GalaxyGamingBoy/6502-Microcontroller/imgs/case-0.png

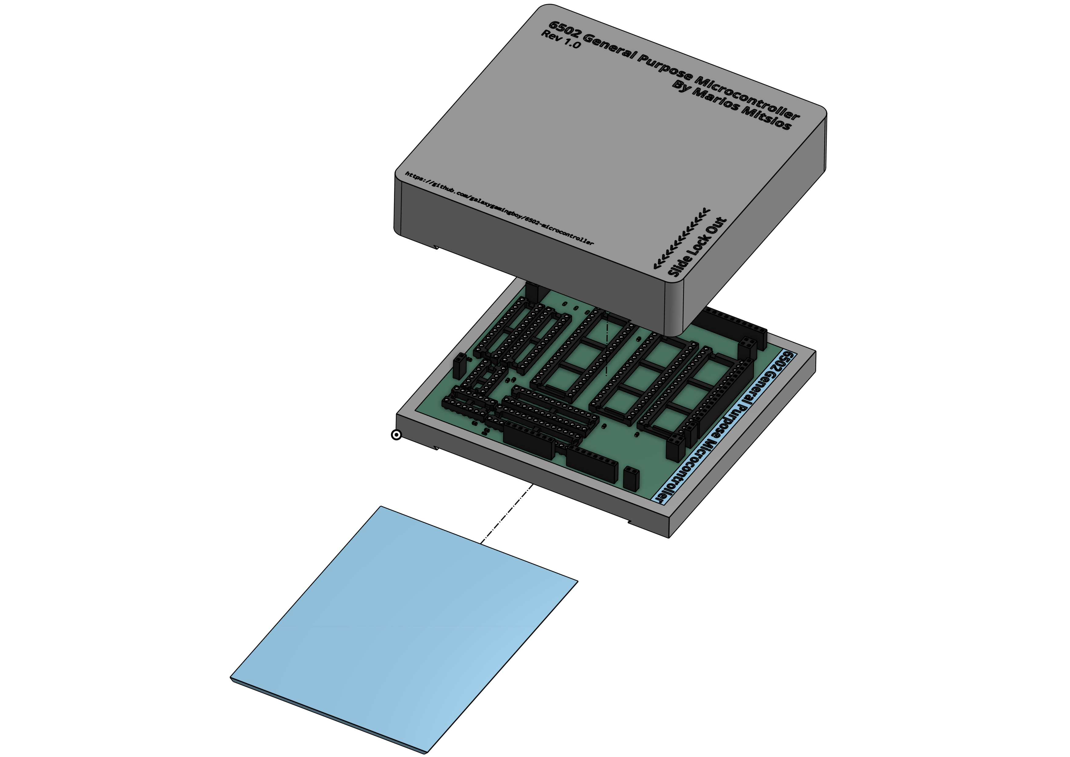
imgs/case-0.png
