GalaxyGamingBoy/6502-Microcontroller/imgs/schematic-0.png

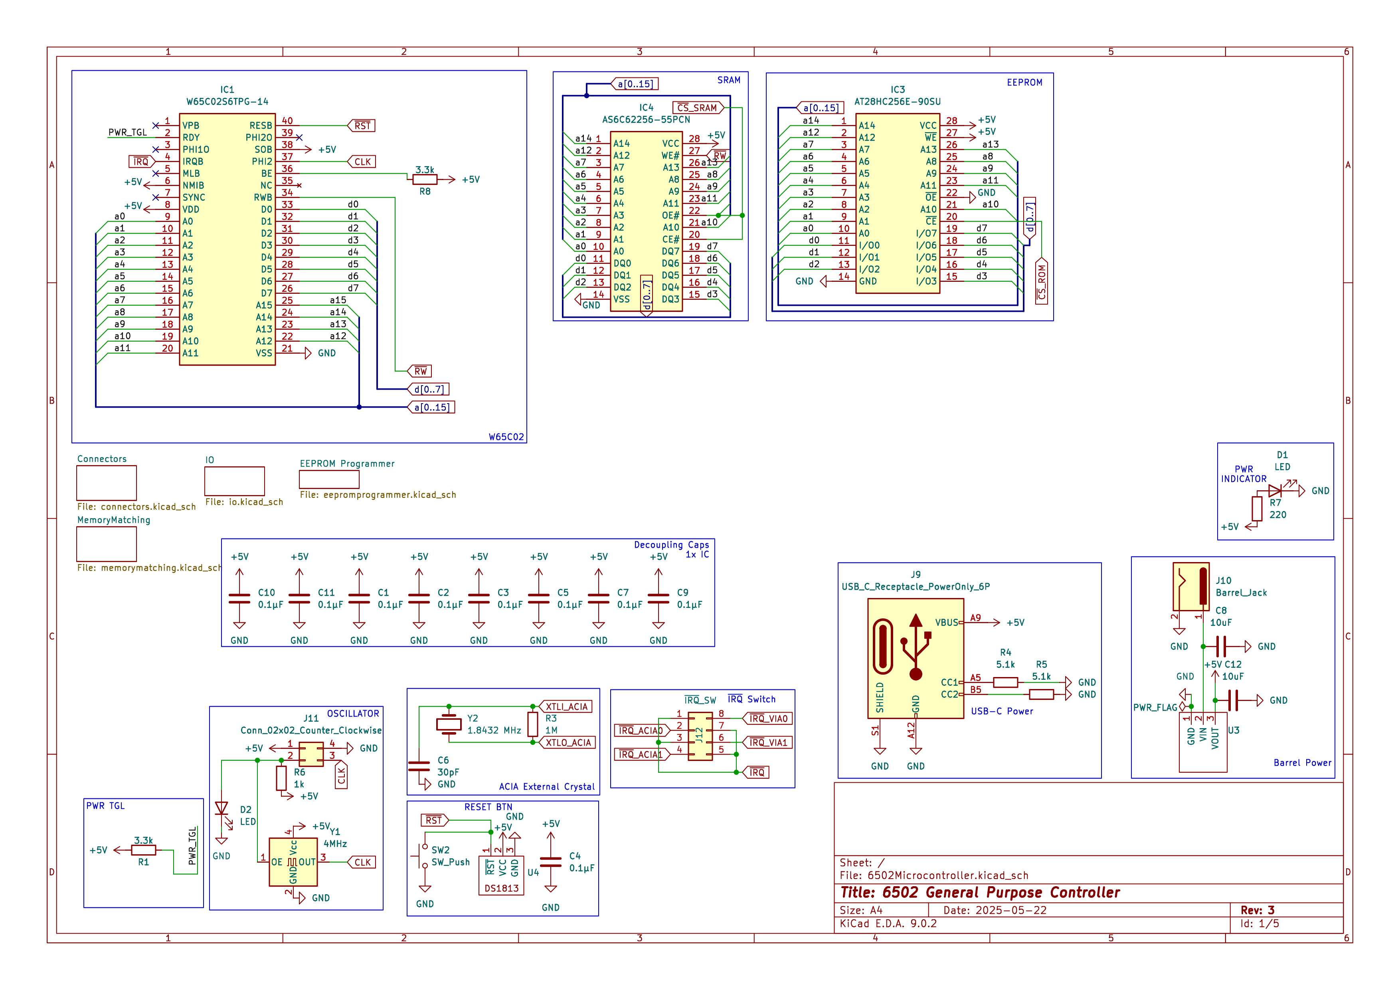
imgs/schematic-0.png
