GalaxyGamingBoy/6502-Microcontroller/imgs/journal/j-2.png

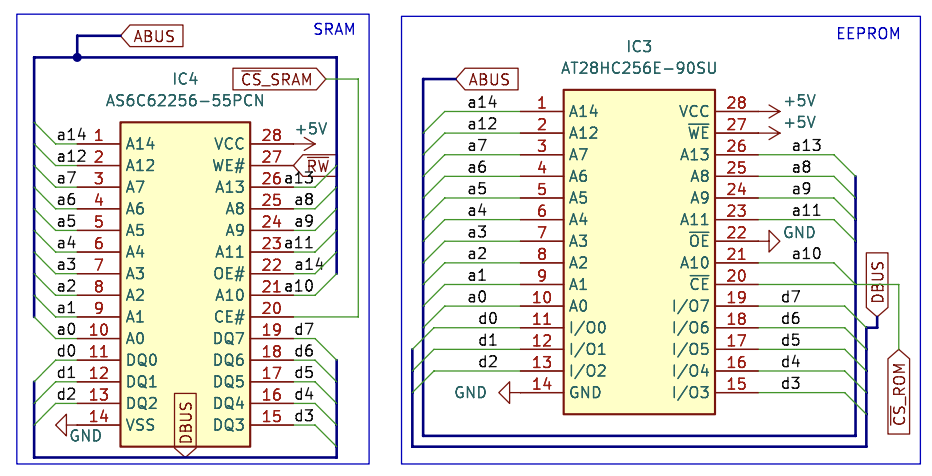
imgs/journal/j-2.png
