GalaxyGamingBoy/6502-Microcontroller/imgs/journal/j-3.png

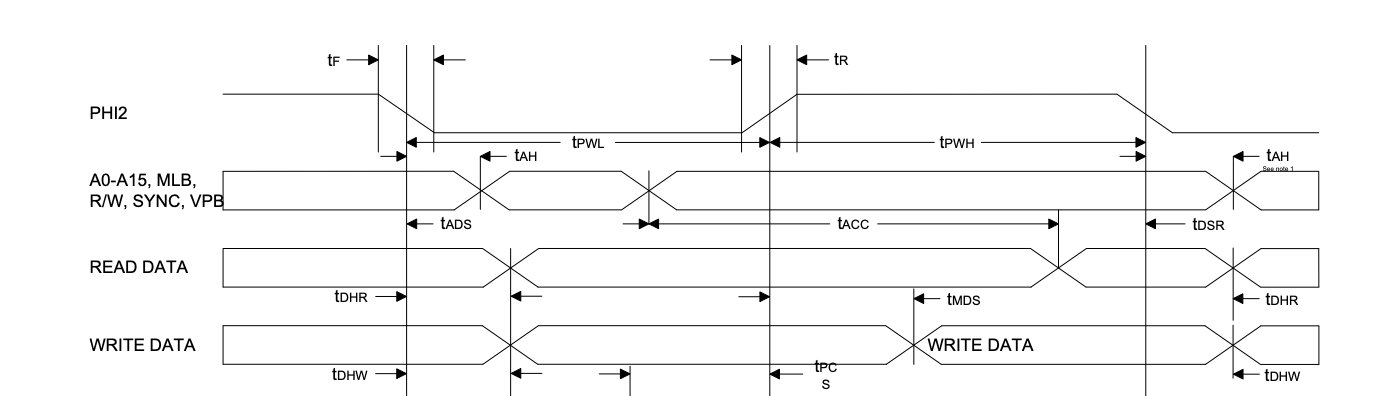
imgs/journal/j-3.png
