GalaxyGamingBoy/6502-Microcontroller/imgs/journal/j-4.png

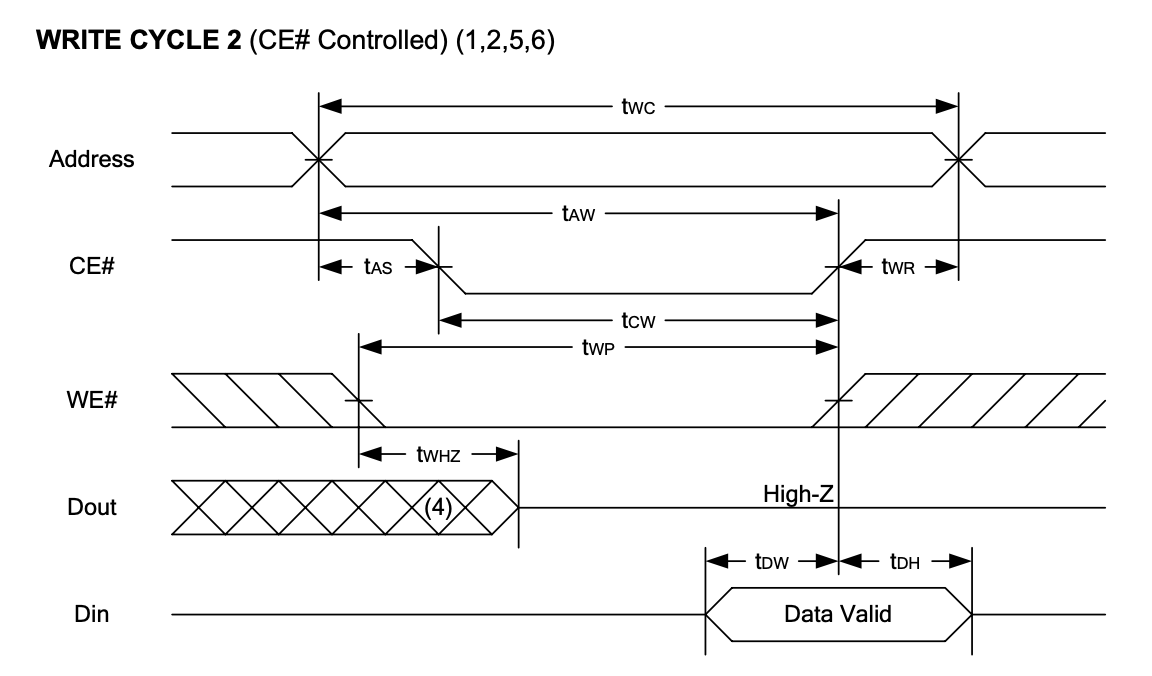
imgs/journal/j-4.png
