GalaxyGamingBoy/6502-Microcontroller/imgs/journal/j-11.png

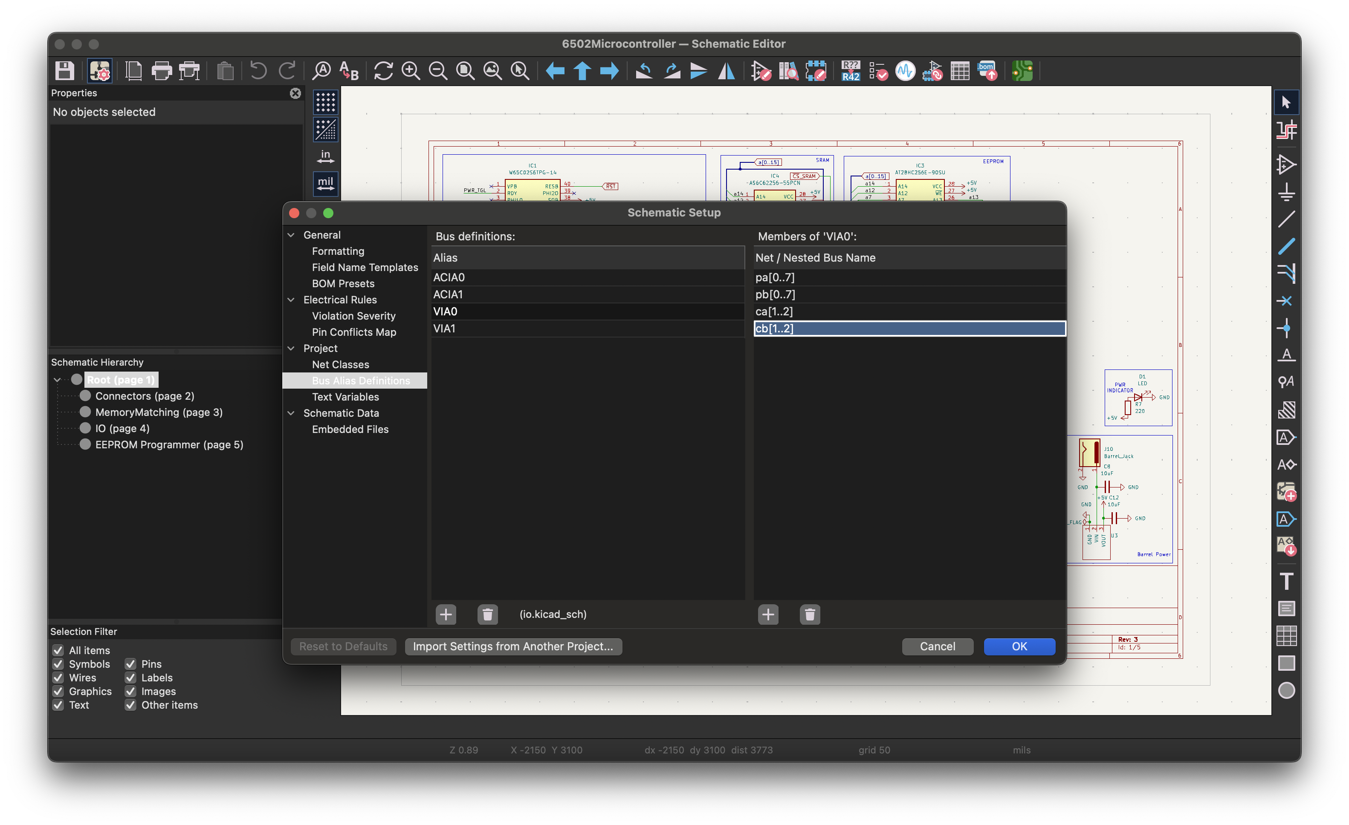
imgs/journal/j-11.png
