GalaxyGamingBoy/6502-Microcontroller/imgs/journal/j-12.png

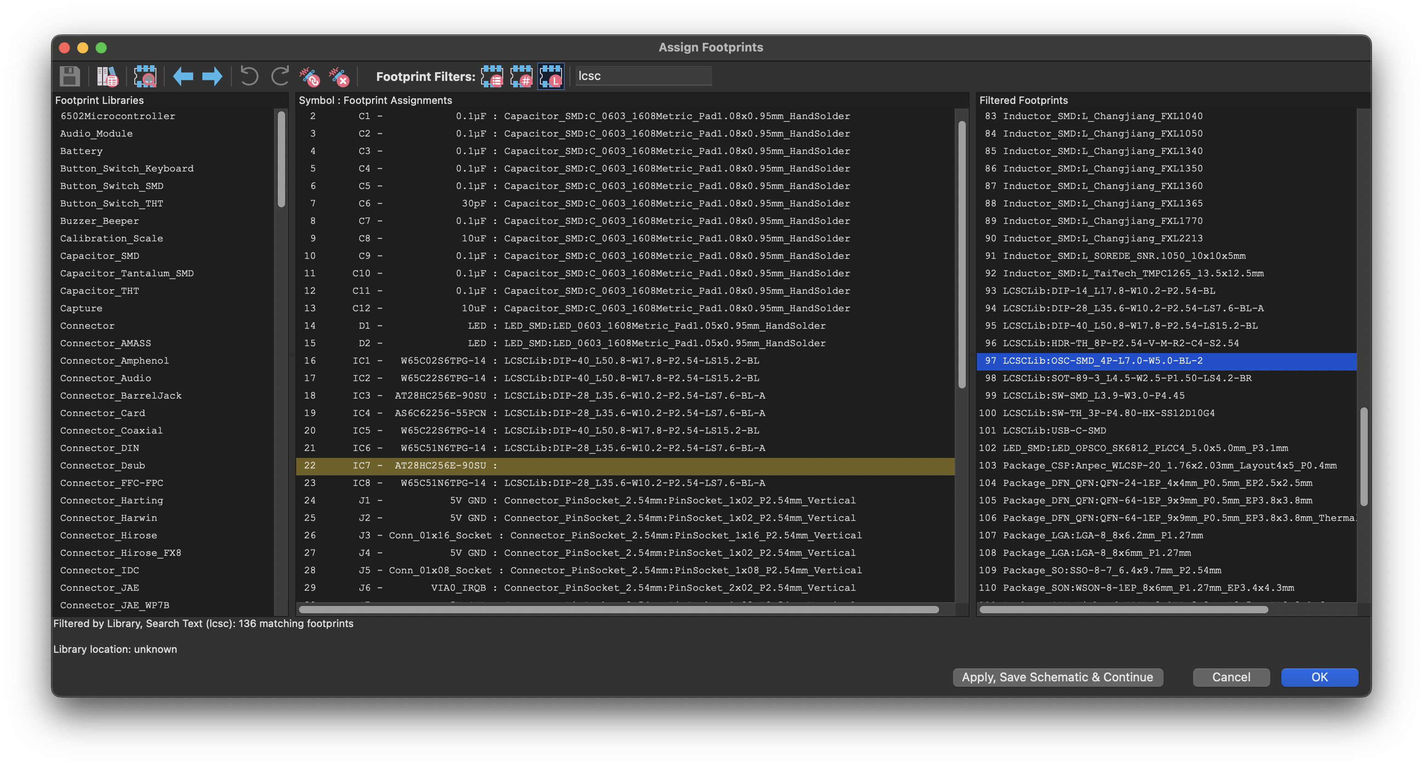
imgs/journal/j-12.png
