GalaxyGamingBoy/6502-Microcontroller/imgs/journal/j-14.png

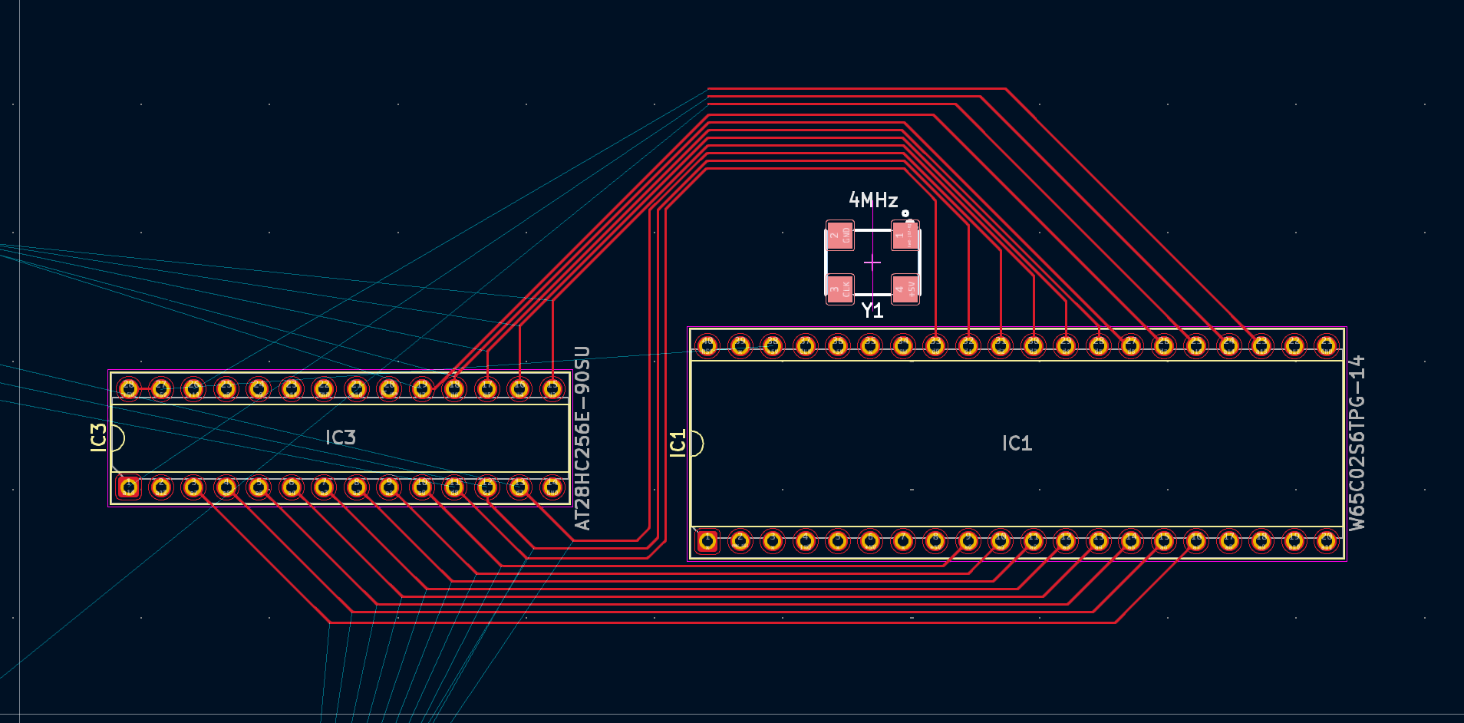
imgs/journal/j-14.png
