GalaxyGamingBoy/6502-Microcontroller/imgs/journal/j-16.png

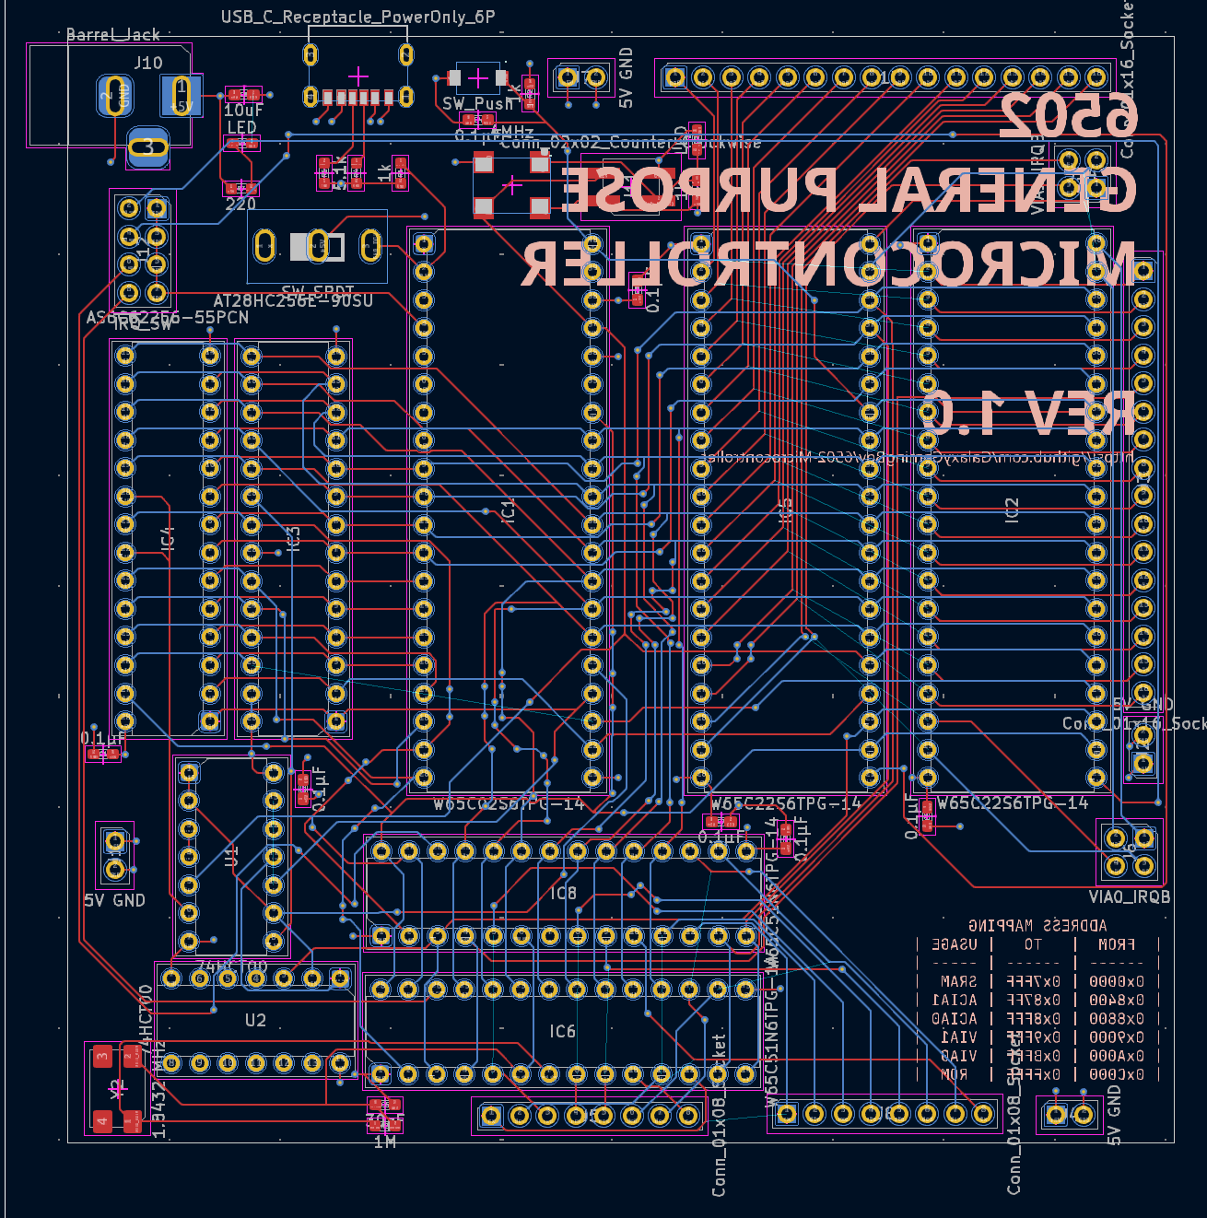
imgs/journal/j-16.png
