GalaxyGamingBoy/6502-Microcontroller/imgs/journal/j-17.png

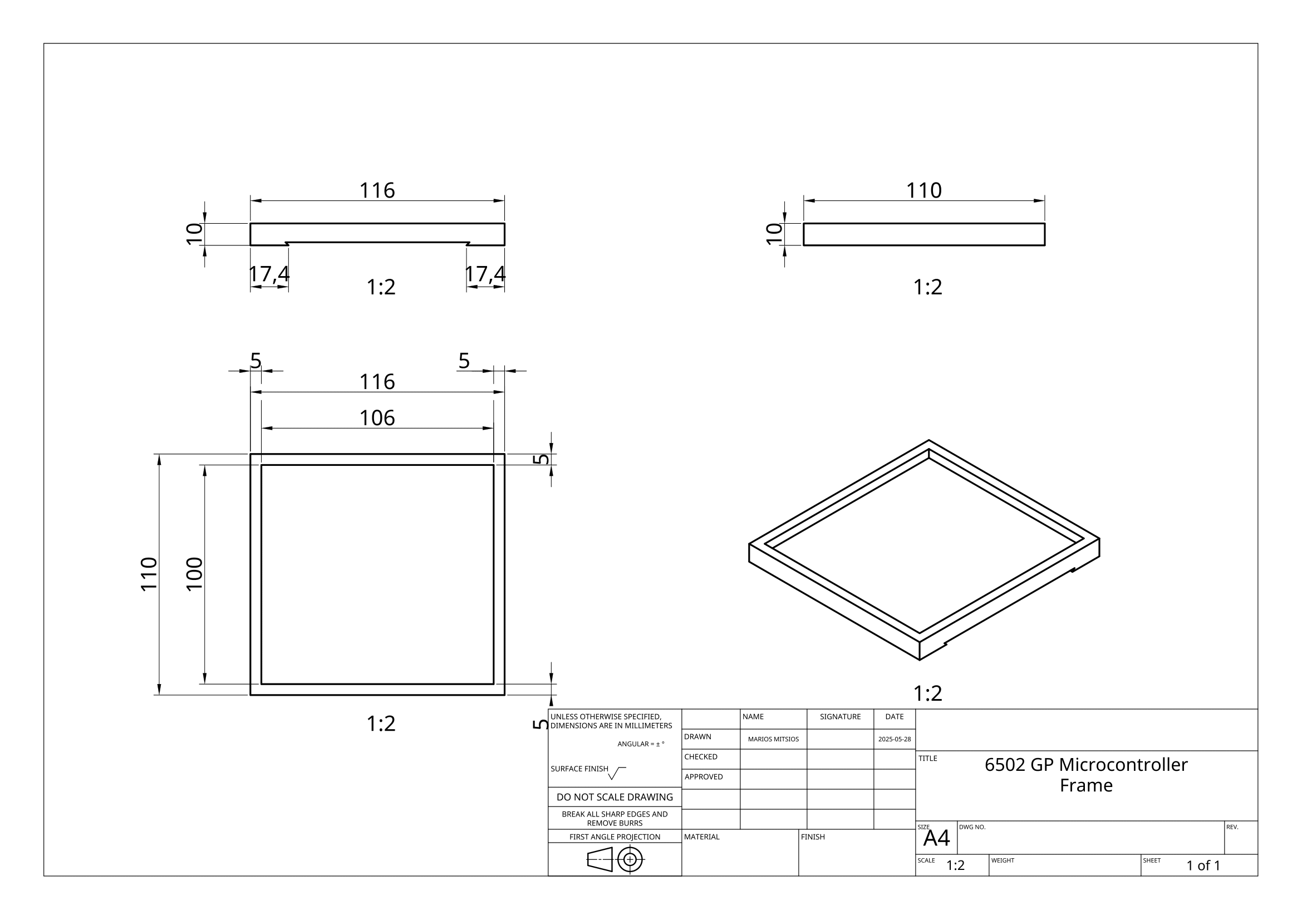
imgs/journal/j-17.png
