GalaxyGamingBoy/6502-Microcontroller/imgs/journal/j-18.png

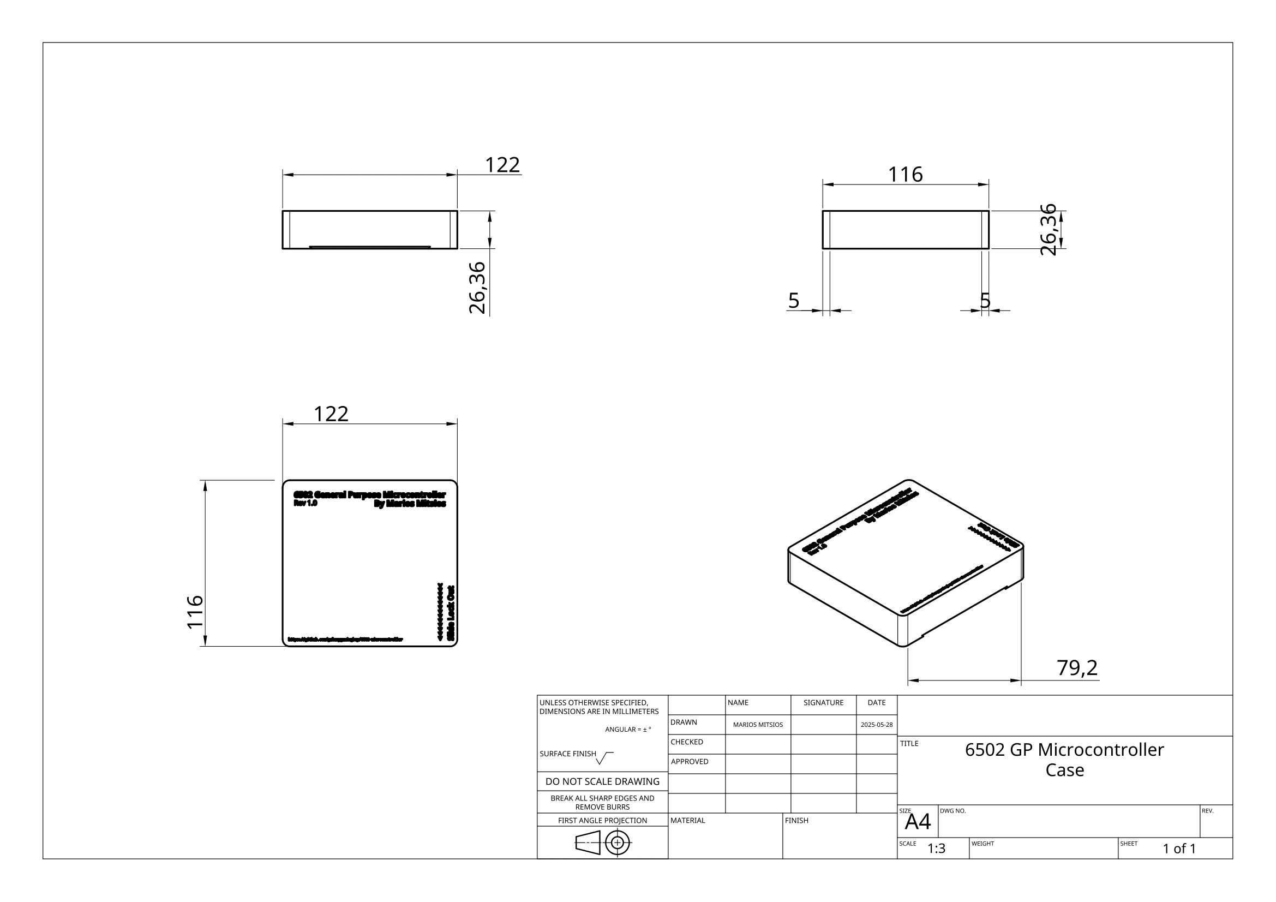
imgs/journal/j-18.png
