GalaxyGamingBoy/6502-Microcontroller/imgs/journal/j-19.png

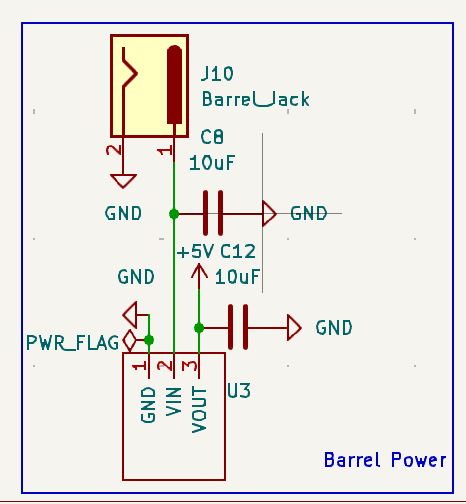
imgs/journal/j-19.png
