GalaxyGamingBoy/6502-Microcontroller/imgs/journal/j-20.png

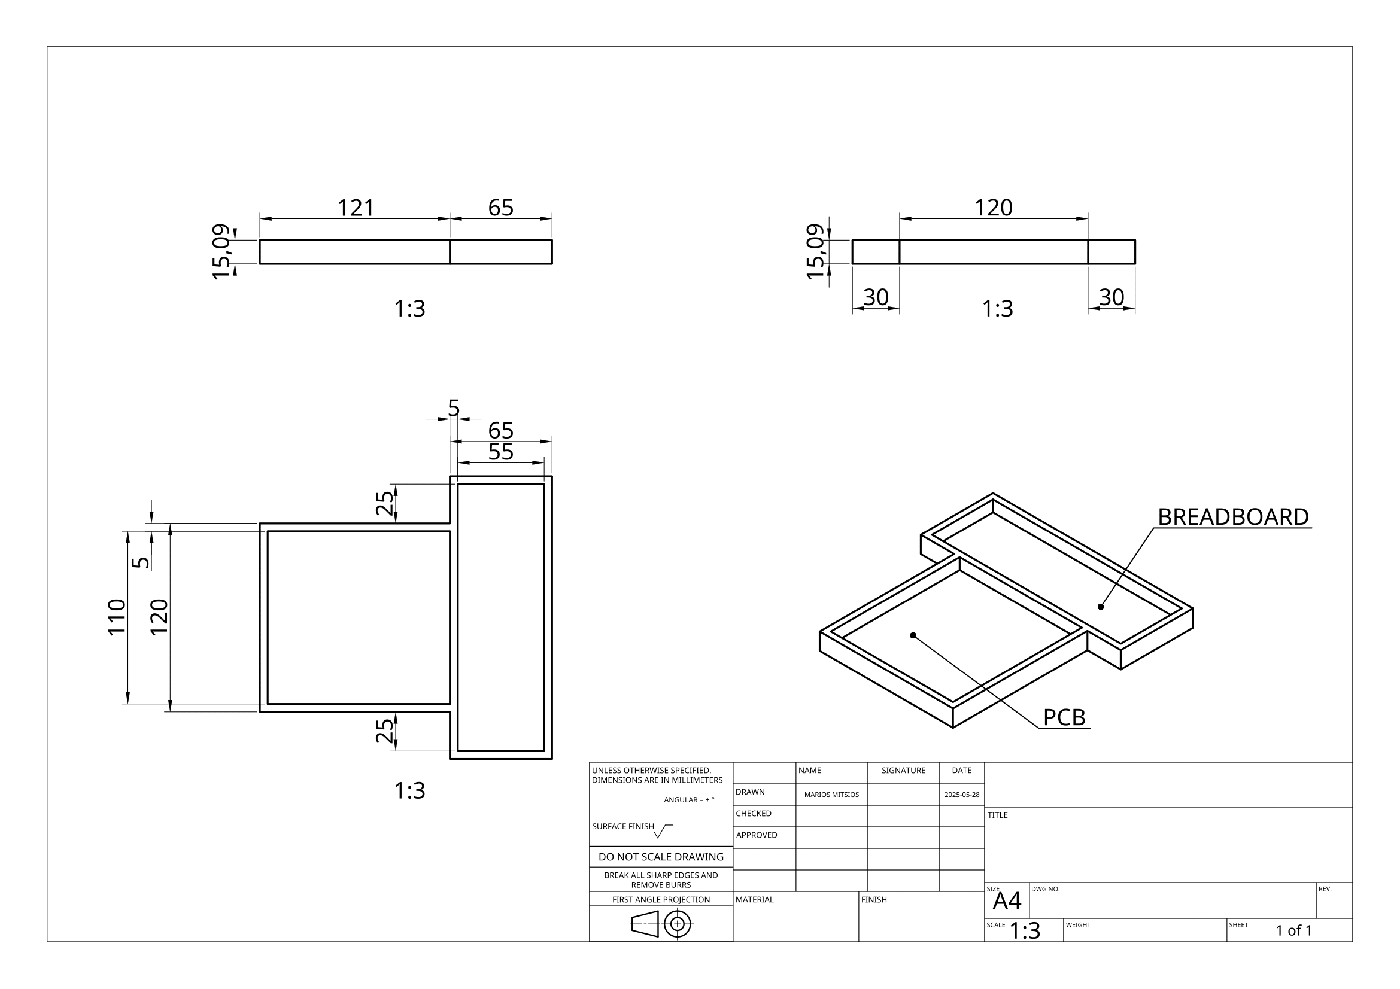
imgs/journal/j-20.png
