GalaxyGamingBoy/6502-Microcontroller/imgs/journal/j-21.png

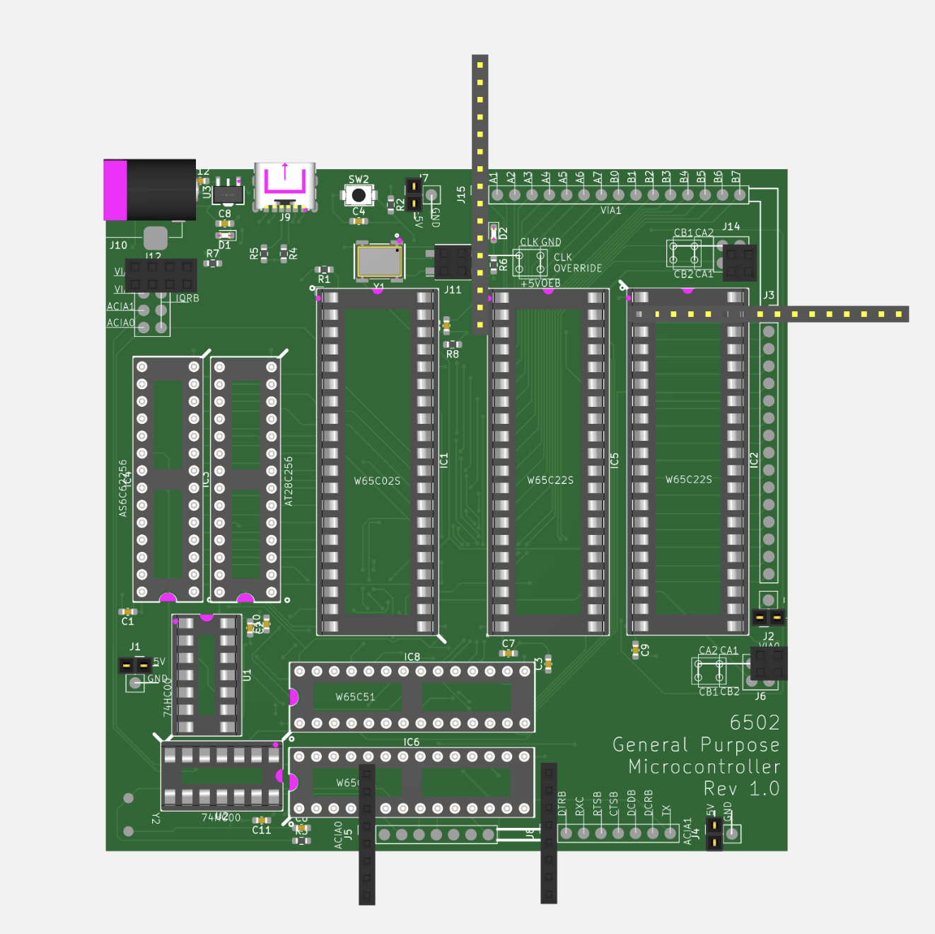
imgs/journal/j-21.png
