GalaxyGamingBoy/6502-Microcontroller/imgs/journal/j-22.png

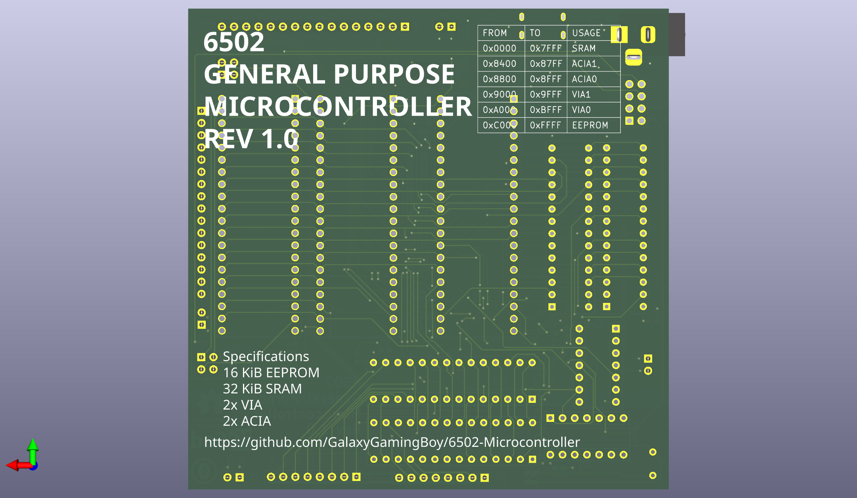
imgs/journal/j-22.png
